ARMmbed/reference-design-RD2166/DAPLink/DAPule-LPC11U35-v1.2.0-BOTTOM.pdf

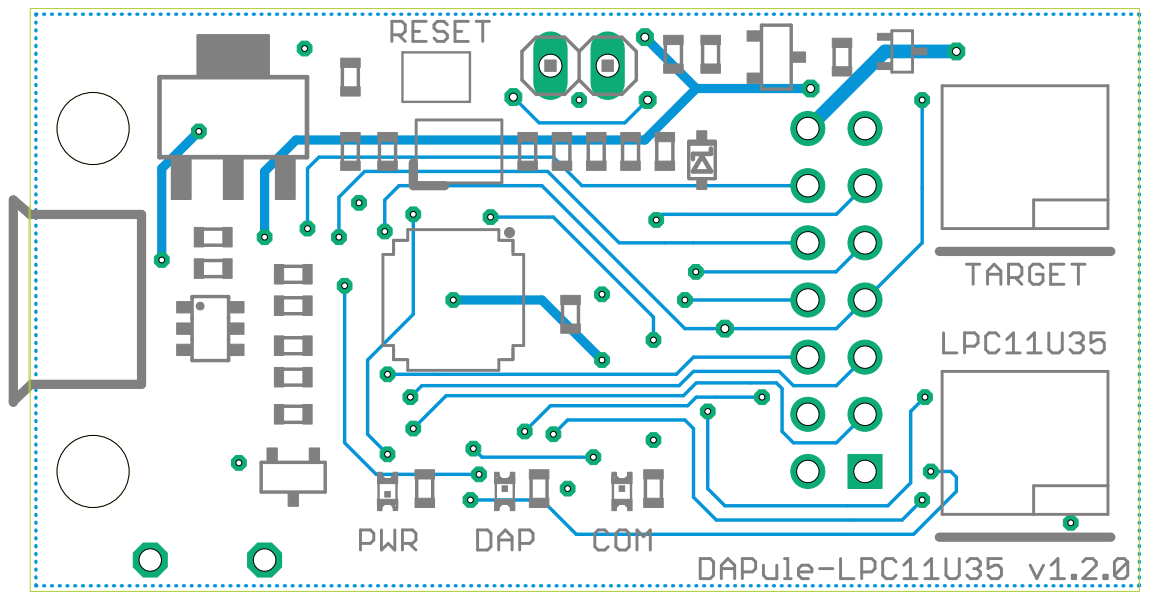
[picture p20: page 1]
