ARMmbed/reference-design-RD2166/DAPLink/DAPule-LPC11U35-v1.2.0-BRD.pdf

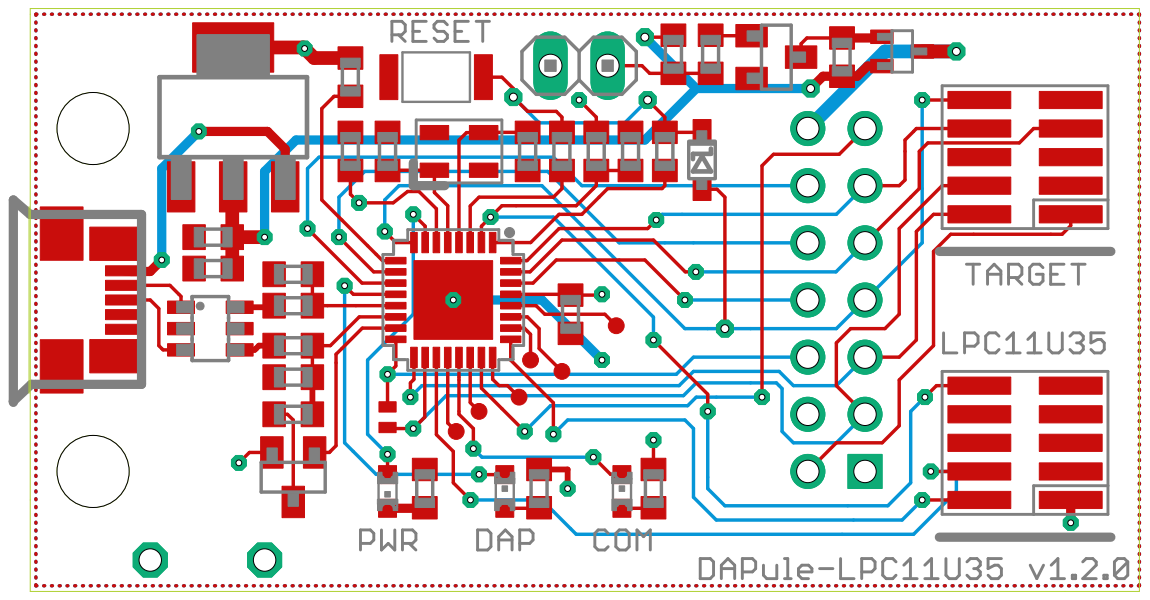
[picture p21: page 1]
