ARMmbed/reference-design-RD2166/DAPLink/DAPule-LPC11U35-v1.2.0-MAP.pdf

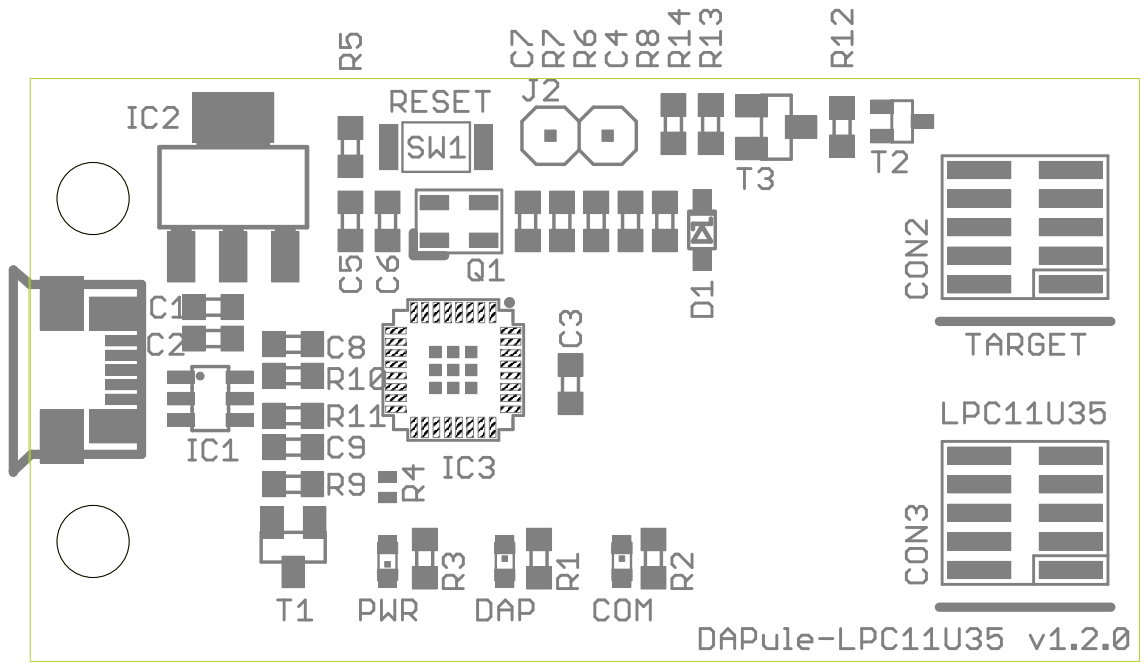
[picture p22: page 1]
