ARMmbed/reference-design-RD2166/DAPLink/DAPule-LPC11U35-v1.2.0-SCH.pdf

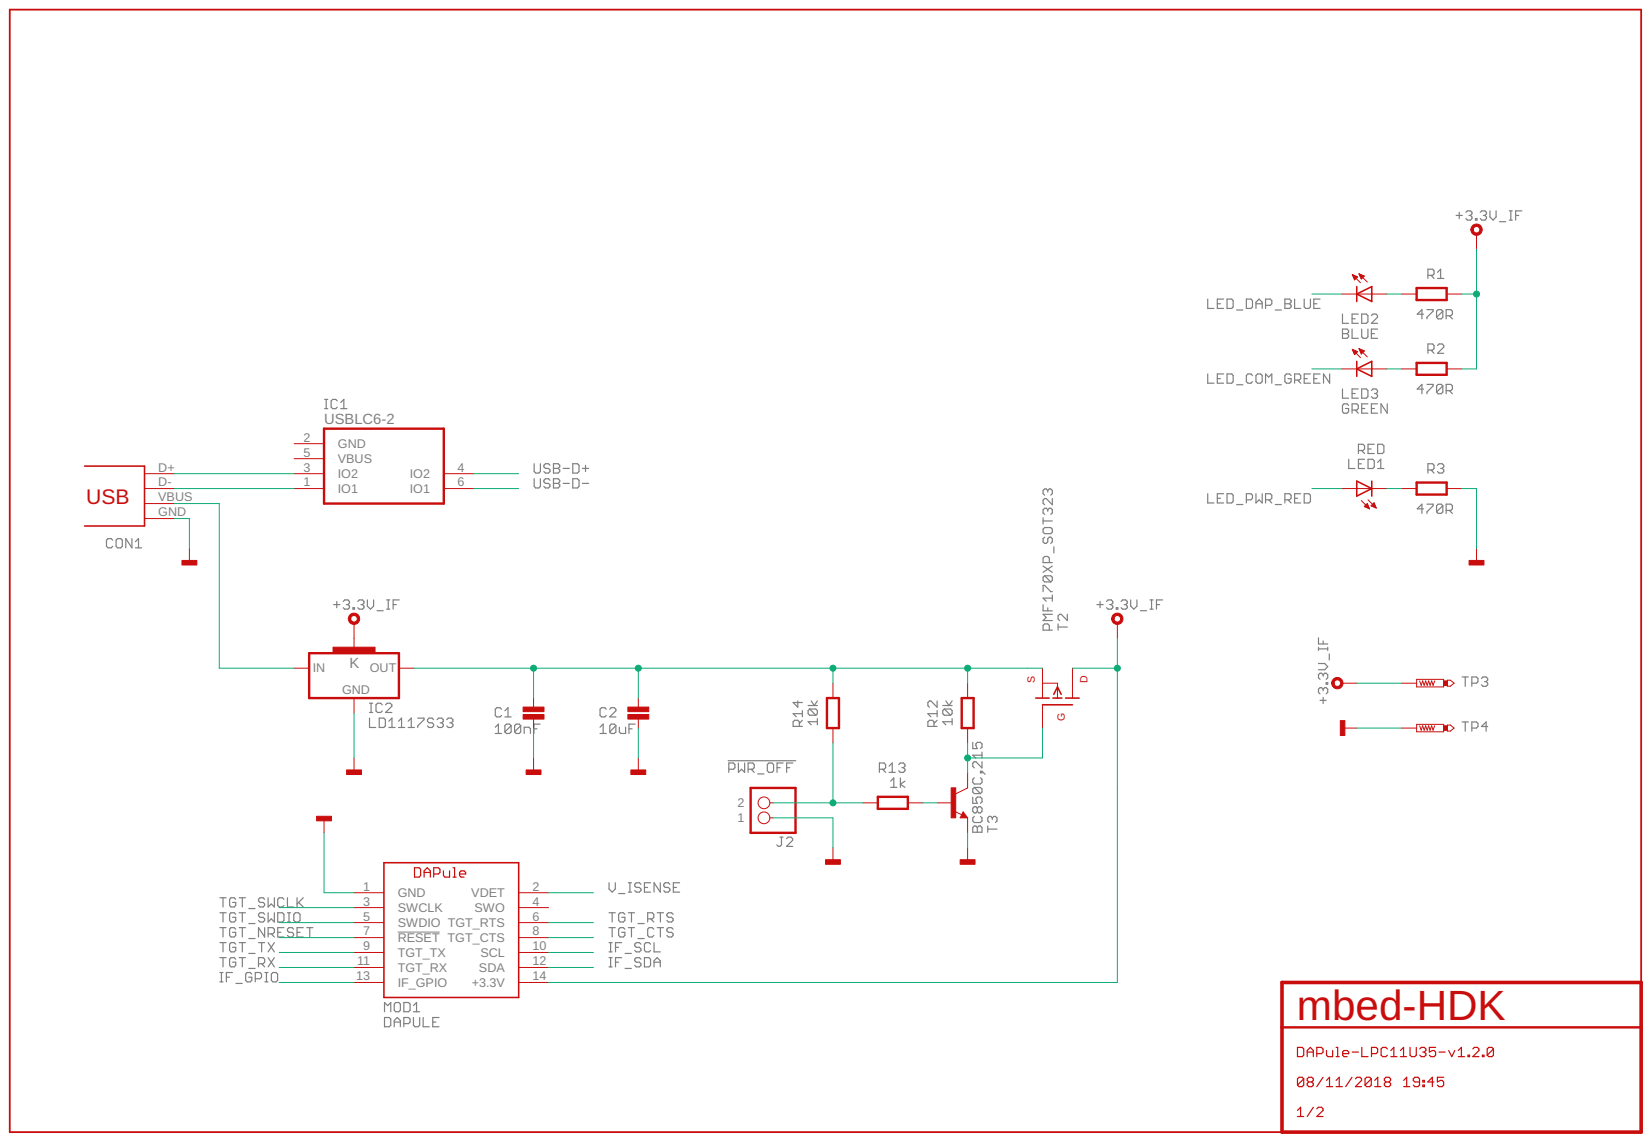
[picture p23: page 1]

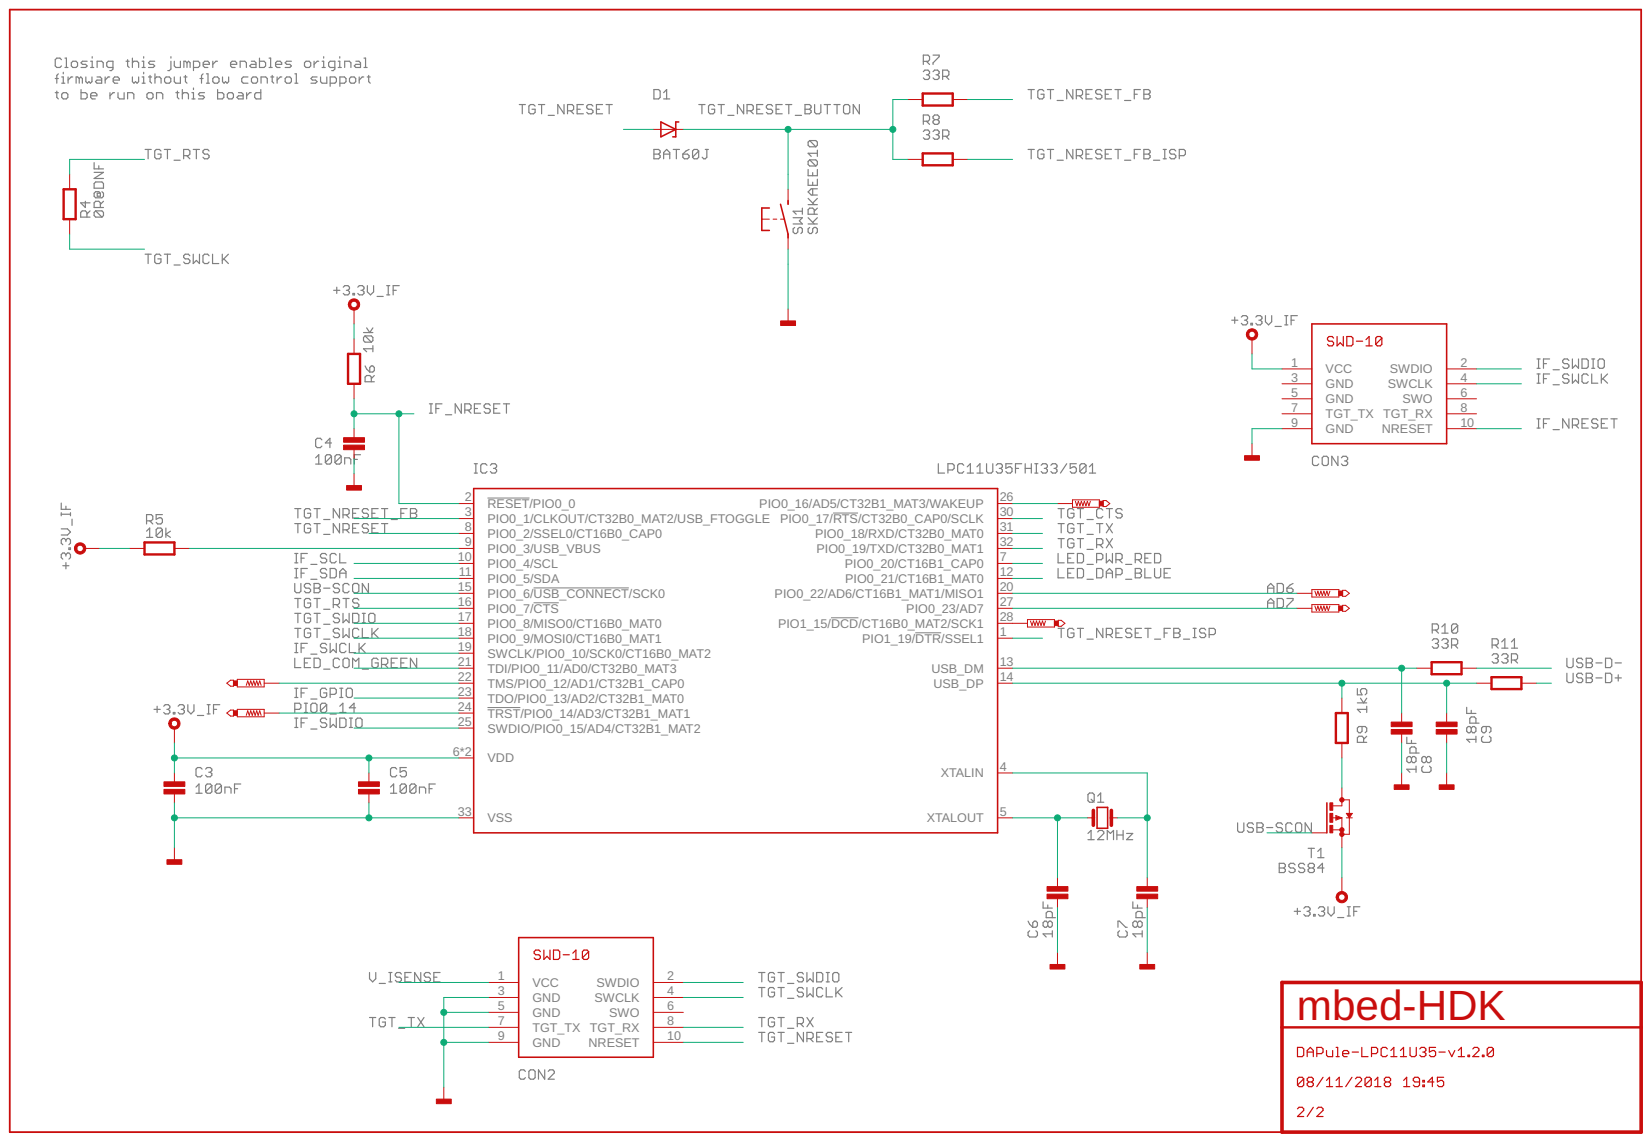
[picture p24: page 2]
