ARMmbed/reference-design-RD2166/DAPLink/DAPule-LPC11U35-v1.2.0-TOP.pdf

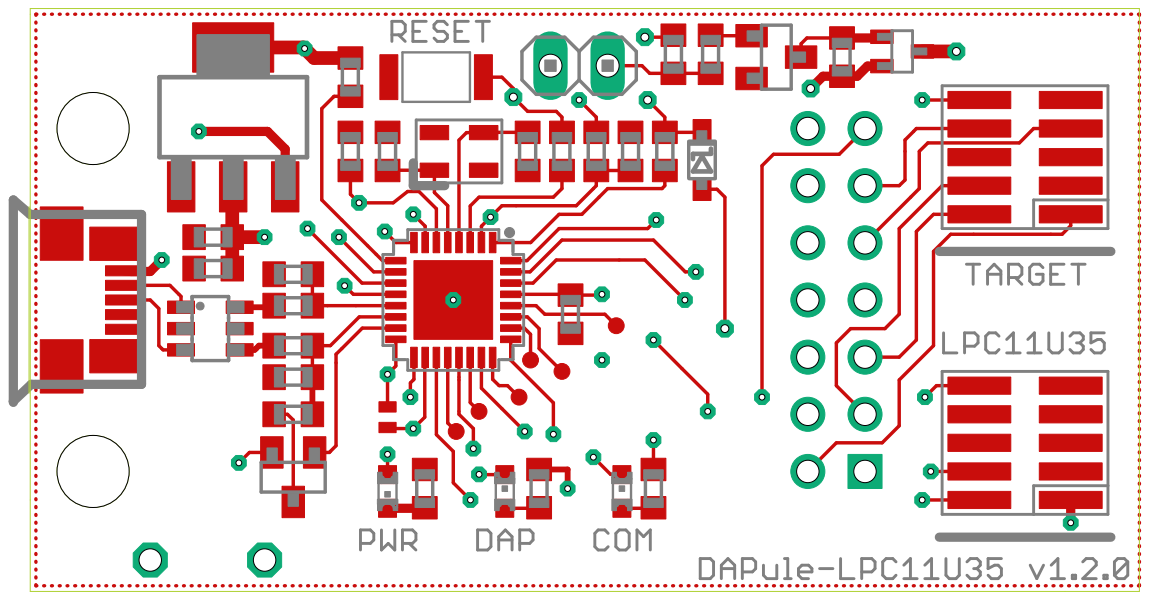
[picture p25: page 1]
