ARMmbed/reference-design-RD2166/Hardware/Reference_Schematic/RD2166-v1.0.0.sch

## EAGLE design Hardware/Reference_Schematic/RD2166-v1.0.0.sch (2019-02-27)

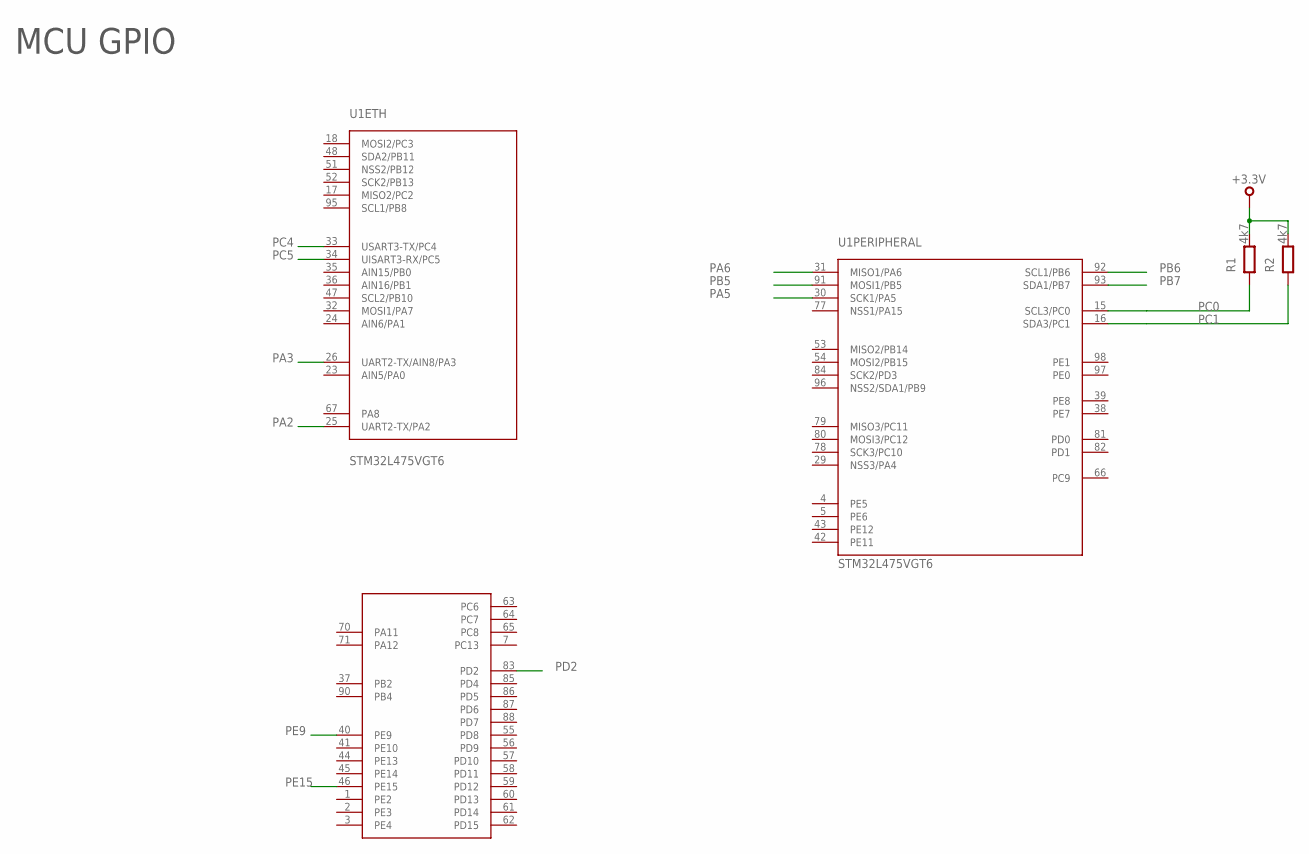
[picture p42: schematic RD2166-v1.0.0.sch, sheet 1]

Parts:
R1, R2: 4k7; 0603
U1: STM32L475VGT6; QFP50P1600X1600X160-100N

Connections:
+3.3V: R1.2, R2.2
PA2: U1.25 (UART2-TX/PA2)
PA3: U1.26 (UART2-TX/AIN8/PA3)
PA5: U1.30 (SCK1/PA5)
PA6: U1.31 (MISO1/PA6)
PB5: U1.91 (MOSI1/PB5)
PB6: U1.92 (SCL1/PB6)
PB7: U1.93 (SDA1/PB7)
PC0: R1.1, U1.15 (SCL3/PC0)
PC1: R2.1, U1.16 (SDA3/PC1)
PC4: U1.33 (USART3-TX/PC4)
PC5: U1.34 (UISART3-RX/PC5)
PD2: U1.83 (PD2)
PE9: U1.40 (PE9)
PE15: U1.46 (PE15)

Notes on the sheet:
MCU GPIO

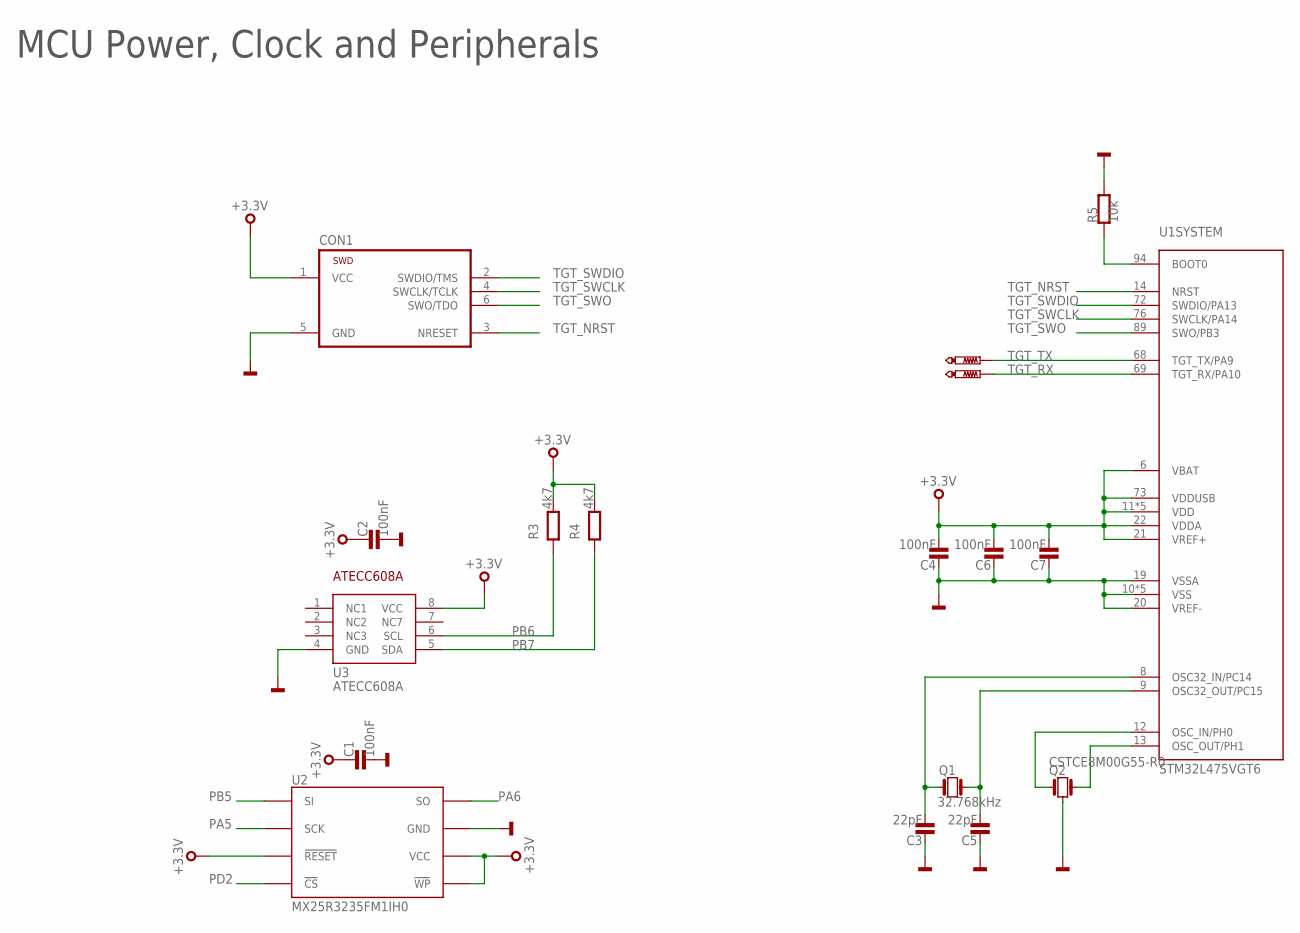
[picture p43: schematic RD2166-v1.0.0.sch, sheet 2]

Parts:
C1, C2, C4, C6, C7: 100nF; 0603
C3, C5: 22pF; 0603
CON1: TC2030-CTX-NL
Q1: 32.768kHz; FC135
Q2: CSTCE8M00G55-R0
R3, R4: 4k7; 0603
R5: 10k; 0603
TP1, TP2: PTR1TP06R; TP06R
U1: STM32L475VGT6; QFP50P1600X1600X160-100N
U2: MX25R3235FM1IH0; SO8
U3: ATECC608A; SO8

Connections:
+3.3V: C1.1, C2.1, C4.2, C6.2, C7.2, CON1.1 (VCC), R3.2, R4.2, U1.6 (VBAT), U1.11 (VDD), U1.21 (VREF+), U1.22 (VDDA), U1.73 (VDDUSB), U2.3 (!WP), U2.7 (!RESET), U2.8 (VCC), U3.8 (VCC)
GND: C1.2, C2.2, C3.1, C4.1, C5.1, C6.1, C7.1, CON1.5 (GND), Q2.2, R5.2, U1.10 (VSS), U1.19 (VSSA), U1.20 (VREF-), U2.4 (GND), U3.4 (GND)
unnamed: R5.1, U1.94 (BOOT0)
unnamed: Q2.1, U1.12 (OSC_IN/PH0)
unnamed: Q2.3, U1.13 (OSC_OUT/PH1)
unnamed: C5.2, Q1.X2 (2), U1.9 (OSC32_OUT/PC15)
unnamed: C3.2, Q1.X1 (1), U1.8 (OSC32_IN/PC14)
PA5: U2.6 (SCK)
PA6: U2.2 (SO)
PB5: U2.5 (SI)
PB6: R3.1, U3.6 (SCL)
PB7: R4.1, U3.5 (SDA)
PD2: U2.1 (!CS)
TGT_NRST: CON1.3 (NRESET), U1.14 (NRST)
TGT_RX: TP2.TP, U1.69 (TGT_RX/PA10)
TGT_SWCLK: CON1.4 (SWCLK/TCLK), U1.76 (SWCLK/PA14)
TGT_SWDIO: CON1.2 (SWDIO/TMS), U1.72 (SWDIO/PA13)
TGT_SWO: CON1.6 (SWO/TDO), U1.89 (SWO/PB3)
TGT_TX: TP1.TP, U1.68 (TGT_TX/PA9)

Notes on the sheet:
MCU Power, Clock and Peripherals

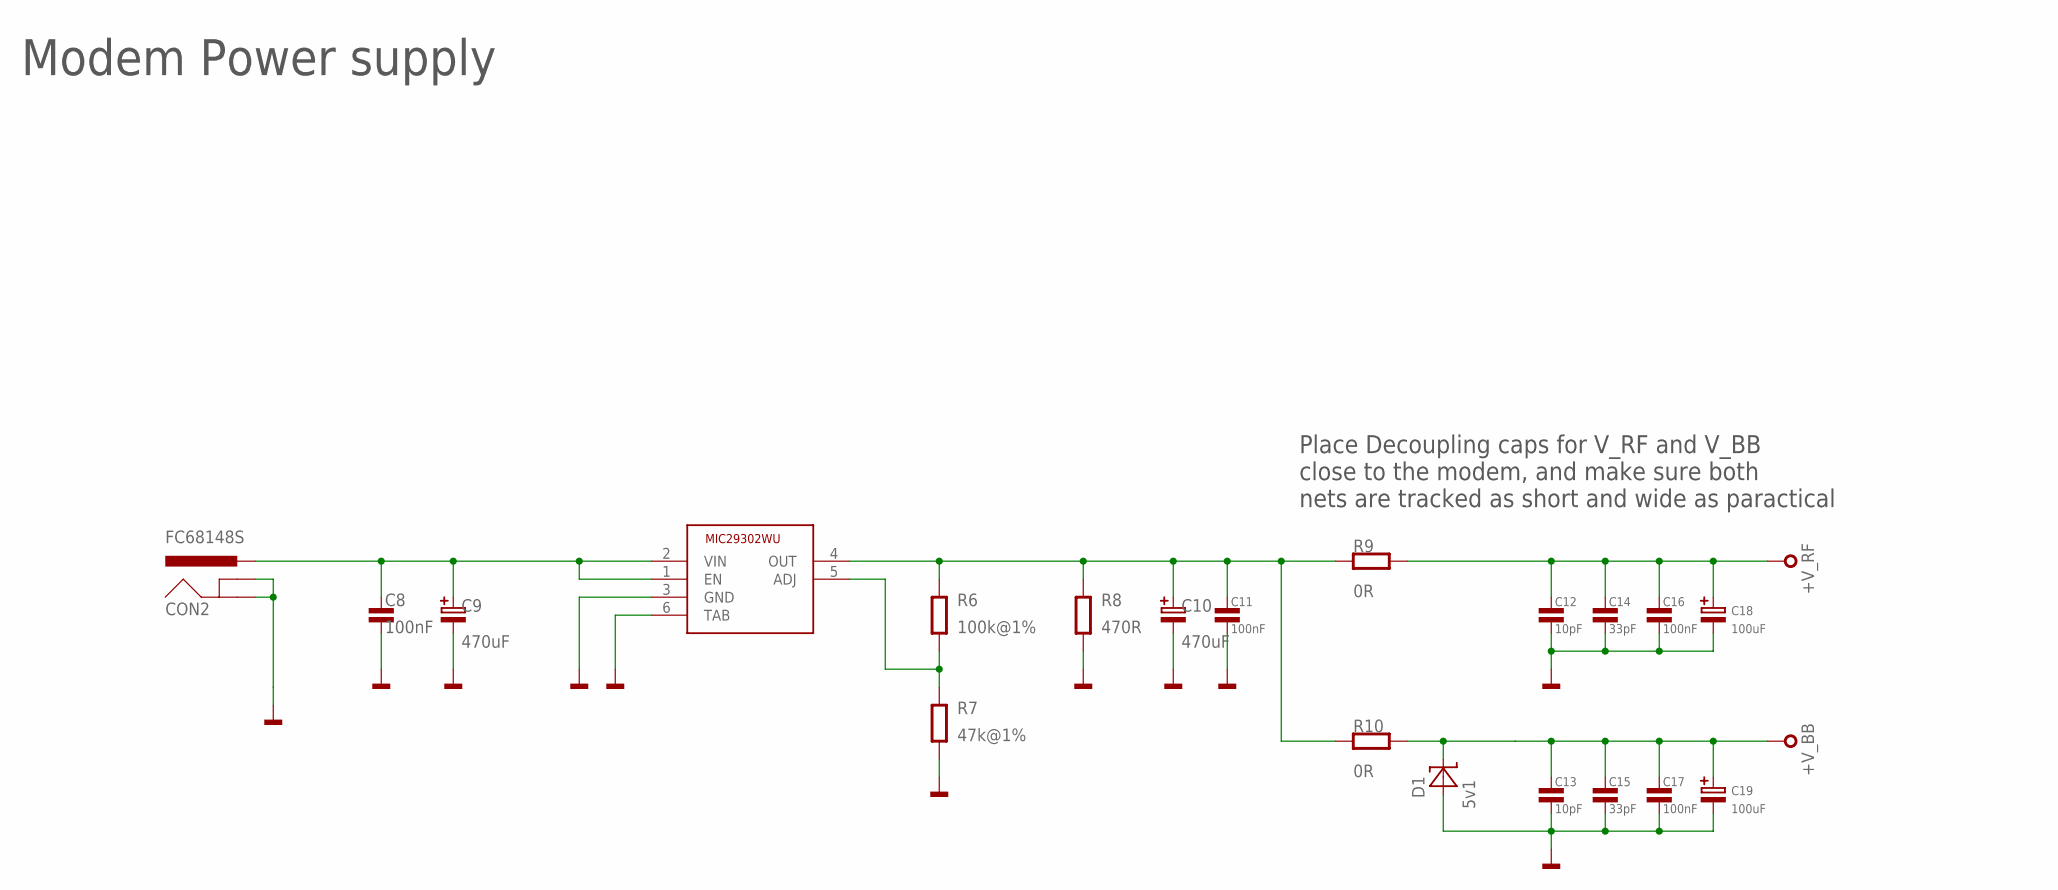
[picture p44: schematic RD2166-v1.0.0.sch, sheet 3]

Parts:
C8, C11, C16, C17: 100nF; 0603
C9, C10: 470uF; PANASONIC_G
C12, C13: 10pF; 0603
C14, C15: 33pF; 0603
C18, C19: 100uF; SMC_A
CON2: FC68148S
D1: 5v1; SOD123
IC1: MIC29302WU; TO263-5
R6: 100k@1%; 0603
R7: 47k@1%; 0603
R8: 470R; 0603
R9, R10: 0R; 0603

Connections:
+V_BB: C13.1, C15.1, C17.1, C19.+, D1.2 (C), R10.2
+V_RF: C12.1, C14.1, C16.1, C18.+, R9.2
GND: C8.2, C9.-, C10.-, C11.2, C12.2, C13.2, C14.2, C15.2, C16.2, C17.2, C18.-, C19.-, CON2.2 (GNDBREAK), CON2.3 (GND), D1.1 (A), IC1.3 (GND), IC1.6 (TAB), R7.1, R8.1
unnamed: C8.1, C9.+, CON2.1-1 (PWR), IC1.1 (EN), IC1.2 (VIN)
unnamed: IC1.5 (ADJ), R6.1, R7.2
unnamed: C10.+, C11.1, IC1.4 (OUT), R6.2, R8.2, R9.1, R10.1

Notes on the sheet:
Modem Power supply
Place Decoupling caps for V_RF and V_BB close to the modem, and make sure both nets are tracked as short and wide as paractical

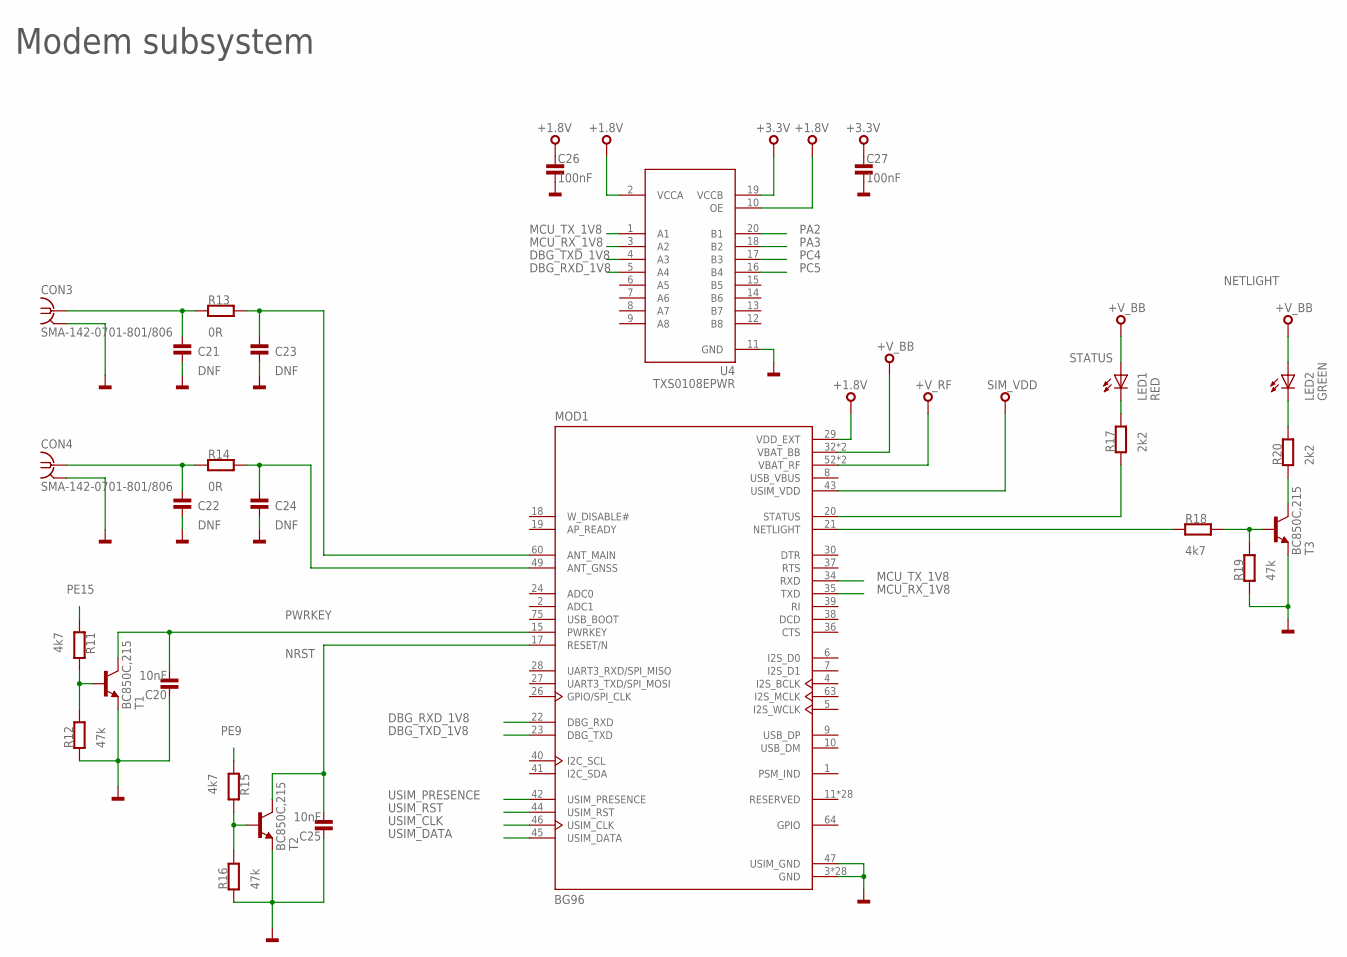
[picture p45: schematic RD2166-v1.0.0.sch, sheet 4]

Parts:
C20, C25: 10nF; 0603
C21, C22, C23, C24: DNF; 0603
C26, C27: 100nF; 0603
CON3, CON4: SMA-142-0701-801/806; J502-ND-142-0701-801/806
LED1: RED; CHIPLED_0603
LED2: GREEN; CHIPLED_0603
MOD1: BG96; LTE_MODULE_BG96
R11, R15, R18: 4k7; 0603
R12, R16, R19: 47k; 0603
R13, R14: 0R; 0603
R17, R20: 2k2; 0603
T1, T2, T3: BC850C,215; SOT23-3
U4: TXS0108EPWR; TSSOP-20

Connections:
+1.8V: C26.1, MOD1.29 (VDD_EXT), U4.2 (VCCA), U4.10 (OE)
+3.3V: C27.1, U4.19 (VCCB)
+V_BB: LED1.A, LED2.A, MOD1.32 (VBAT_BB)
+V_RF: MOD1.52 (VBAT_RF)
DBG_RXD_1V8: MOD1.22 (DBG_RXD), U4.5 (A4)
DBG_TXD_1V8: MOD1.23 (DBG_TXD), U4.4 (A3)
GND: C20.1, C21.1, C22.1, C23.1, C24.1, C25.1, C26.2, C27.2, CON3.G@1 (2), CON4.G@1 (2), MOD1.3 (GND), MOD1.47 (USIM_GND), R12.1, R16.1, R19.1, T1.2 (E), T2.2 (E), T3.2 (E), U4.11 (GND)
MCU_RX_1V8: MOD1.35 (TXD), U4.3 (A2)
MCU_TX_1V8: MOD1.34 (RXD), U4.1 (A1)
unnamed: LED1.C, R17.2
unnamed: LED2.C, R20.2
unnamed: C21.2, CON3.1, R13.1
unnamed: C23.2, MOD1.60 (ANT_MAIN), R13.2
unnamed: C22.2, CON4.1, R14.1
unnamed: C24.2, MOD1.49 (ANT_GNSS), R14.2
unnamed: R11.2, R12.2, T1.1 (B)
unnamed: R15.2, R16.2, T2.1 (B)
unnamed: R18.2, R19.2, T3.1 (B)
NETLIGHT: MOD1.21 (NETLIGHT), R18.1
NRST: C25.2, MOD1.17 (RESET/N), T2.3 (C)
NRST1: R20.1, T3.3 (C)
PA2: U4.20 (B1)
PA3: U4.18 (B2)
PC4: U4.17 (B3)
PC5: U4.16 (B4)
PE9: R15.1
PE15: R11.1
PWRKEY: C20.2, MOD1.15 (PWRKEY), T1.3 (C)
SIM_VDD: MOD1.43 (USIM_VDD)
STATUS: MOD1.20 (STATUS), R17.1
USIM_CLK: MOD1.46 (USIM_CLK)
USIM_DATA: MOD1.45 (USIM_DATA)
USIM_PRESENCE: MOD1.42 (USIM_PRESENCE)
USIM_RST: MOD1.44 (USIM_RST)

Notes on the sheet:
Modem subsystem

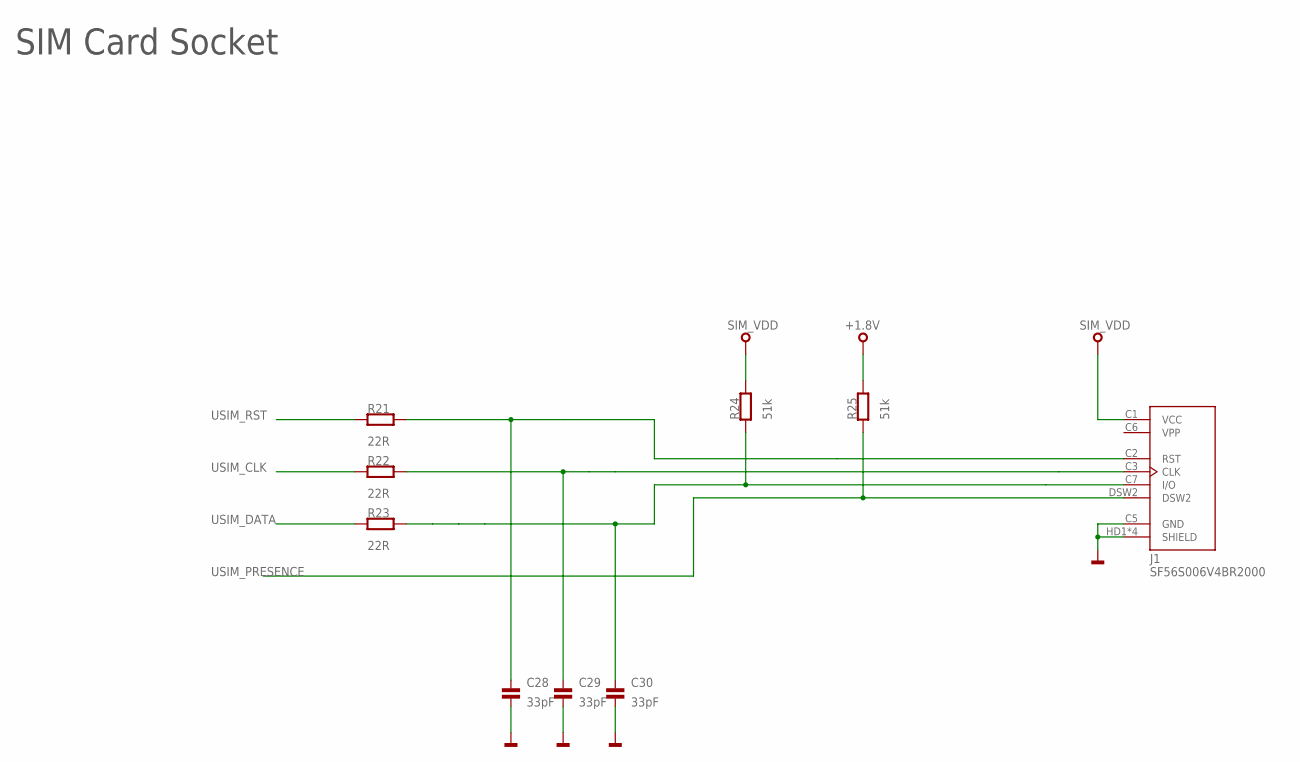
[picture p46: schematic RD2166-v1.0.0.sch, sheet 5]

Parts:
C28, C29, C30: 33pF; 0603
J1: SF56S006V4BR2000; JAE_SF56S006V4BR2000
R21, R22, R23: 22R; 0603
R24, R25: 51k; 0603

Connections:
+1.8V: R25.2
GND: C28.2, C29.2, C30.2, J1.C5 (GND), J1.HD1 (SHIELD)
unnamed: C28.1, J1.C2 (RST), R21.2
unnamed: C29.1, J1.C3 (CLK), R22.2
unnamed: C30.1, J1.C7 (I/O), R23.2, R24.1
SIM_VDD: J1.C1 (VCC), R24.2
USIM_CLK: R22.1
USIM_DATA: R23.1
USIM_PRESENCE: J1.DSW2, R25.1
USIM_RST: R21.1

Notes on the sheet:
SIM Card Socket
