ARMmbed/reference-design-RD2166/update_default_resources.c

//----------------------------------------------------------------------------
//   The confidential and proprietary information contained in this file may
//   only be used by a person authorised under and to the extent permitted
//   by a subsisting licensing agreement from ARM Limited or its affiliates.
//
//          (C) COPYRIGHT 2013-2017 ARM Limited or its affiliates.
//              ALL RIGHTS RESERVED
//
//   This entire notice must be reproduced on all copies of this file
//   and copies of this file may only be made by a person if such person is
//   permitted to do so under the terms of a subsisting license agreement
//   from ARM Limited or its affiliates.
//----------------------------------------------------------------------------

#ifdef MBED_CLOUD_CLIENT_USER_CONFIG_FILE
#include MBED_CLOUD_CLIENT_USER_CONFIG_FILE
#endif

#include <stdint.h>

#ifdef MBED_CLOUD_DEV_UPDATE_ID
const uint8_t arm_uc_vendor_id[] = {
    0xfa, 0x6b, 0x4a, 0x53, 0xd5, 0xad, 0x5f, 0xdf, 0xbe, 0x9d, 0xe6, 0x63, 0xe4, 0xd4, 0x1f, 0xfe
};
const uint16_t arm_uc_vendor_id_size = sizeof(arm_uc_vendor_id);

const uint8_t arm_uc_class_id[]  = {
    0xa6, 0xf3, 0x6e, 0x63, 0x33, 0xb2, 0x55, 0x18, 0xa5, 0xbc, 0xf5, 0xeb, 0xee, 0x1b, 0xa9, 0xe0
};
const uint16_t arm_uc_class_id_size = sizeof(arm_uc_class_id);
#endif

#ifdef MBED_CLOUD_DEV_UPDATE_CERT
const uint8_t arm_uc_default_fingerprint[] =  {
    0x73, 0xc, 0x14, 0xaa, 0xd6, 0x3, 0x3e, 0x38, 0x1b, 0xe7, 0xce, 0x55, 0xb0, 0xaa, 0x59, 0xe4,
    0x94, 0x83, 0x15, 0xb8, 0x47, 0x39, 0x35, 0xbf, 0xa0, 0x45, 0x39, 0xcf, 0xa6, 0xf8, 0x27, 0x93
};
const uint16_t arm_uc_default_fingerprint_size =
    sizeof(arm_uc_default_fingerprint);

const uint8_t arm_uc_default_subject_key_identifier[] =  {
    0x18, 0xef, 0xe6, 0x6b, 0x97, 0x2c, 0x3, 0x9b, 0x8d, 0xd4, 0xb6, 0xed, 0xdc, 0x62, 0x6e, 0x1c,
    0xf6, 0x79, 0x4f, 0x53
};
const uint16_t arm_uc_default_subject_key_identifier_size =
    sizeof(arm_uc_default_subject_key_identifier);

const uint8_t arm_uc_default_certificate[] = {
    0x30, 0x82, 0x1, 0x7e, 0x30, 0x82, 0x1, 0x25, 0xa0, 0x3, 0x2, 0x1, 0x2, 0x2, 0x14, 0x7e,
    0x68, 0xbc, 0x9f, 0xba, 0x56, 0x84, 0x8f, 0x66, 0x7, 0x71, 0xba, 0xe4, 0x89, 0x2a, 0x55, 0x7,
    0xf2, 0x1a, 0xb8, 0x30, 0xa, 0x6, 0x8, 0x2a, 0x86, 0x48, 0xce, 0x3d, 0x4, 0x3, 0x2, 0x30,
    0x12, 0x31, 0x10, 0x30, 0xe, 0x6, 0x3, 0x55, 0x4, 0x3, 0xc, 0x7, 0x61, 0x72, 0x6d, 0x2e,
    0x63, 0x6f, 0x6d, 0x30, 0x1e, 0x17, 0xd, 0x31, 0x39, 0x30, 0x31, 0x33, 0x31, 0x31, 0x37, 0x30,
    0x39, 0x34, 0x36, 0x5a, 0x17, 0xd, 0x31, 0x39, 0x30, 0x35, 0x30, 0x31, 0x31, 0x37, 0x30, 0x39,
    0x34, 0x36, 0x5a, 0x30, 0x12, 0x31, 0x10, 0x30, 0xe, 0x6, 0x3, 0x55, 0x4, 0x3, 0xc, 0x7,
    0x61, 0x72, 0x6d, 0x2e, 0x63, 0x6f, 0x6d, 0x30, 0x59, 0x30, 0x13, 0x6, 0x7, 0x2a, 0x86, 0x48,
    0xce, 0x3d, 0x2, 0x1, 0x6, 0x8, 0x2a, 0x86, 0x48, 0xce, 0x3d, 0x3, 0x1, 0x7, 0x3, 0x42,
    0x0, 0x4, 0x32, 0x38, 0x94, 0xbf, 0xdb, 0x0, 0x88, 0x3b, 0x8a, 0x5, 0x5d, 0x7b, 0x3c, 0x7e,
    0xf6, 0x26, 0x45, 0x66, 0xc9, 0x3d, 0xb7, 0xf, 0xf0, 0x6a, 0xc1, 0x8f, 0xbe, 0xfe, 0xdc, 0xa4,
    0x31, 0xc6, 0xea, 0x47, 0x38, 0x9a, 0xec, 0x19, 0x60, 0x49, 0xba, 0x33, 0xdf, 0x11, 0x6, 0x7,
    0x6b, 0x5c, 0x87, 0x89, 0xd6, 0xb4, 0xfa, 0x33, 0xd2, 0x71, 0x0, 0x41, 0x81, 0x90, 0x26, 0x29,
    0x8d, 0x3b, 0xa3, 0x59, 0x30, 0x57, 0x30, 0xb, 0x6, 0x3, 0x55, 0x1d, 0xf, 0x4, 0x4, 0x3,
    0x2, 0x7, 0x80, 0x30, 0x14, 0x6, 0x3, 0x55, 0x1d, 0x11, 0x4, 0xd, 0x30, 0xb, 0x82, 0x9,
    0x6c, 0x6f, 0x63, 0x61, 0x6c, 0x68, 0x6f, 0x73, 0x74, 0x30, 0x13, 0x6, 0x3, 0x55, 0x1d, 0x25,
    0x4, 0xc, 0x30, 0xa, 0x6, 0x8, 0x2b, 0x6, 0x1, 0x5, 0x5, 0x7, 0x3, 0x3, 0x30, 0x1d,
    0x6, 0x3, 0x55, 0x1d, 0xe, 0x4, 0x16, 0x4, 0x14, 0x18, 0xef, 0xe6, 0x6b, 0x97, 0x2c, 0x3,
    0x9b, 0x8d, 0xd4, 0xb6, 0xed, 0xdc, 0x62, 0x6e, 0x1c, 0xf6, 0x79, 0x4f, 0x53, 0x30, 0xa, 0x6,
    0x8, 0x2a, 0x86, 0x48, 0xce, 0x3d, 0x4, 0x3, 0x2, 0x3, 0x47, 0x0, 0x30, 0x44, 0x2, 0x20,
    0x45, 0xe7, 0xd7, 0x98, 0x8e, 0xcb, 0xd1, 0x9f, 0xe7, 0xbb, 0xb8, 0x30, 0x1b, 0x95, 0x90, 0x40,
    0x89, 0xee, 0x8, 0x7, 0xd7, 0x8d, 0x2b, 0x7d, 0x44, 0x4, 0x6c, 0x8b, 0x78, 0xb, 0x0, 0x14,
    0x2, 0x20, 0x71, 0xe7, 0x8e, 0x7c, 0x87, 0x97, 0x1e, 0xd3, 0xa6, 0x3a, 0x70, 0x31, 0xa8, 0xb3,
    0xb0, 0xef, 0xb4, 0x25, 0xc3, 0xf3, 0xca, 0xbe, 0x13, 0xce, 0x8, 0xf, 0x1f, 0x22, 0x2d, 0xc9,
    0xb8, 0xaf
};
const uint16_t arm_uc_default_certificate_size = sizeof(arm_uc_default_certificate);
#endif


#ifdef MBED_CLOUD_DEV_UPDATE_PSK
const uint8_t arm_uc_default_psk[] = {
    
};
const uint8_t arm_uc_default_psk_size = sizeof(arm_uc_default_psk);
const uint16_t arm_uc_default_psk_bits = sizeof(arm_uc_default_psk)*8;

const uint8_t arm_uc_default_psk_id[] = {
    
};
const uint8_t arm_uc_default_psk_id_size = sizeof(arm_uc_default_psk_id);
#endif
